bmcloutier/OnStarduino/resources/models/Housing_Top.3mf

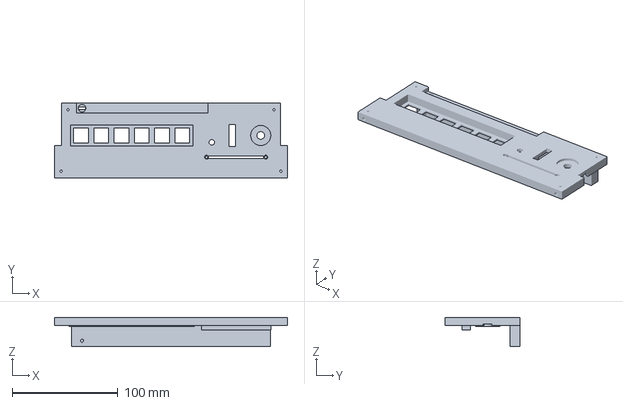
[picture p22: CAD file, 2025-06-04]
resources/models/Housing_Top.3mf
220.0 x 70.5 x 27.5 mm
