bmcloutier/OnStarduino/resources/models/Tuner_BeltHolder.3mf

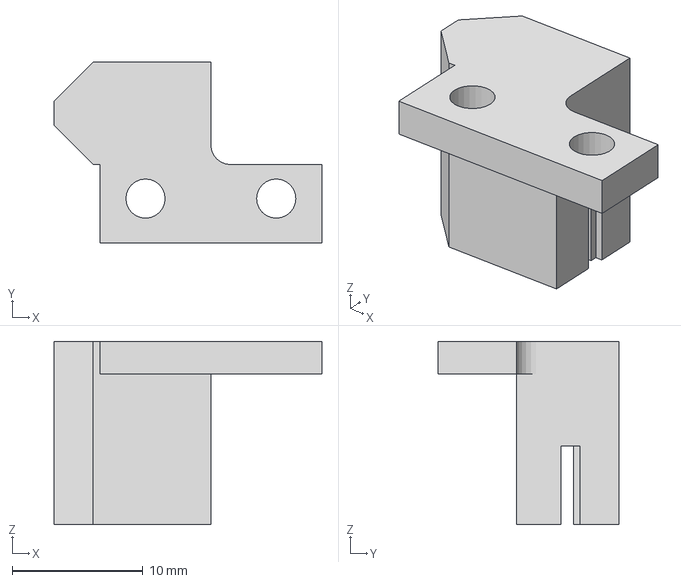
[picture p23: CAD file, 2025-06-04]
resources/models/Tuner_BeltHolder.3mf
20.5 x 13.8 x 14.0 mm
