bmcloutier/OnStarduino/resources/models/Housing_Back.3mf

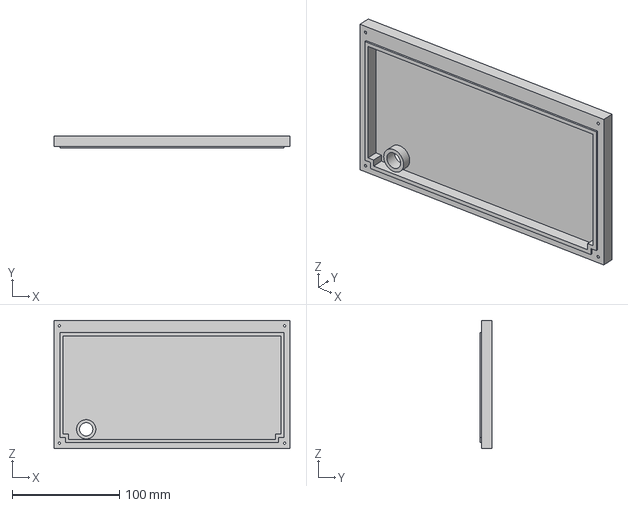
[picture p24: CAD file, 2025-06-04]
resources/models/Housing_Back.3mf
220.0 x 11.0 x 119.5 mm
