bmcloutier/OnStarduino/resources/models/Housing_WindowBorders.3mf

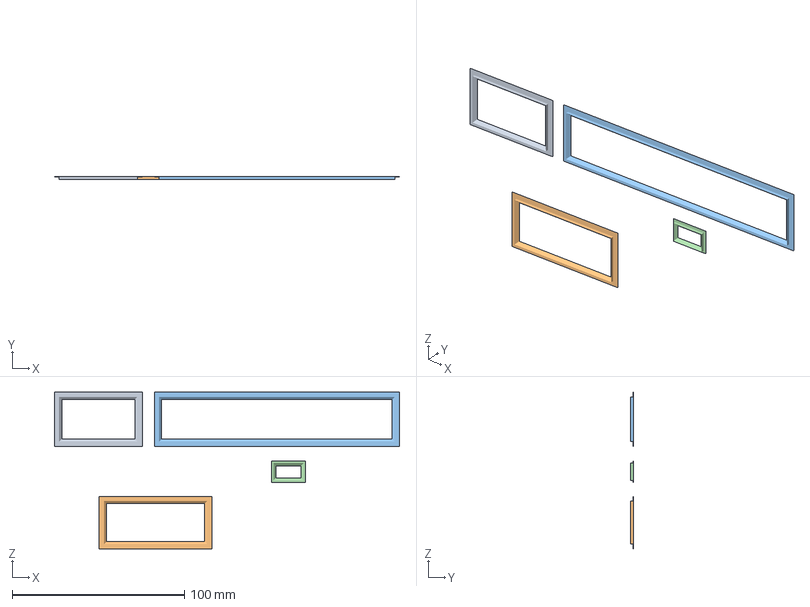
[picture p25: CAD file, 2025-06-04]
resources/models/Housing_WindowBorders.3mf
200.5 x 1.90 x 91.0 mm
